tpetzoldt/growthlab/doc/algenlogger/Wachstumskurve_Versuch01_lr01.png

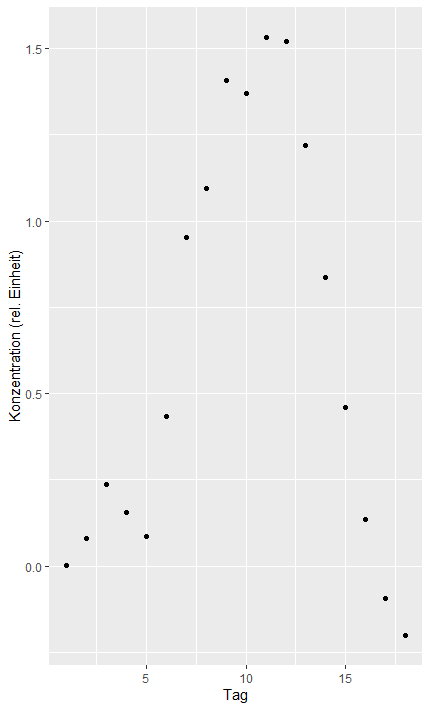
doc/algenlogger/Wachstumskurve_Versuch01_lr01.png
