tpetzoldt/growthlab/doc/arduino-blink.jpg

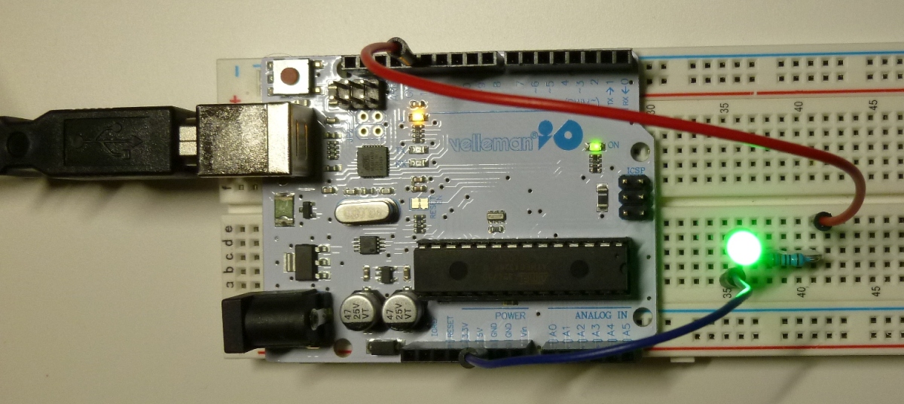
doc/arduino-blink.jpg
